Guru-RF/MicroPico/src/W5100/code.py

import board
import busio
import digitalio
import time
from adafruit_wiznet5k.adafruit_wiznet5k import WIZNET5K

##SPI0
SPI0_RX = board.GP16
SPI0_CSn = board.GP17
SPI0_SCK = board.GP18
SPI0_TX = board.GP19

##reset
W5x00_RSTn = board.GP20

print("Wiznet5k Ping Test (no DHCP)")

# Setup your network configuration below
# random MAC, later should change this value on your vendor ID
MY_MAC = (0x00, 0x03, 0x03, 0x03, 0x04, 0x05)
IP_ADDRESS = (172, 16, 30, 4)
SUBNET_MASK = (255, 255, 255, 0)
GATEWAY_ADDRESS = (172, 16, 30, 1)
DNS_SERVER = (8, 8, 8, 8)

#led = digitalio.DigitalInOut(board.GP25)
#led.direction = digitalio.Direction.OUTPUT

ethernetRst = digitalio.DigitalInOut(W5x00_RSTn)
ethernetRst.direction = digitalio.Direction.OUTPUT

# For Adafruit Ethernet FeatherWing
cs = digitalio.DigitalInOut(SPI0_CSn)
# For Particle Ethernet FeatherWing
# cs = digitalio.DigitalInOut(board.D5)
spi_bus = busio.SPI(SPI0_SCK, MOSI=SPI0_TX, MISO=SPI0_RX)

# Reset W5500 first
ethernetRst.value = False
time.sleep(1)
ethernetRst.value = True

# Initialize ethernet interface with DHCP
# eth = WIZNET5K(spi_bus, cs)
# Initialize ethernet interface without DHCP
eth = WIZNET5K(spi_bus, cs, is_dhcp=False, mac=MY_MAC)

# Set network configuration
eth.ifconfig = (IP_ADDRESS, SUBNET_MASK, GATEWAY_ADDRESS, DNS_SERVER)

print("Chip Version:", eth.chip)
print("MAC Address:", [hex(i) for i in eth.mac_address])
print("My IP address is:", eth.pretty_ip(eth.ip_address))

while True:
#    led.value = not led.value
    time.sleep(1)

print("Done!")
