Guru-RF/MicroPico/src/BME680/code.py

import adafruit_bme680
import time
import busio
import board

# Create the I2C interface.
i2c = busio.I2C(scl=board.GP21, sda=board.GP20)
bme680 = adafruit_bme680.Adafruit_BME680_I2C(i2c)

# change this to match the location's pressure (hPa) at sea level
bme680.sea_level_pressure = 1013.25

while True:
    print("\nTemperature: %0.1f C" % bme680.temperature)
    print("Gas: %d ohm" % bme680.gas)
    print("Humidity: %0.1f %%" % bme680.relative_humidity)
    print("Pressure: %0.3f hPa" % bme680.pressure)
    print("Altitude = %0.2f meters" % bme680.altitude)

    time.sleep(2)
