Guru-RF/MicroPico/src/code.py

import supervisor
import asyncio
import time
import µPICO
import board
import usb_hid
import simpleio
from adafruit_hid.keyboard import Keyboard
from adafruit_hid.keyboard_layout_us import KeyboardLayoutUS
from adafruit_hid.keycode import Keycode
from adafruit_hid.consumer_control import ConsumerControl
from adafruit_hid.consumer_control_code import ConsumerControlCode
from rainbowio import colorwheel

import terminalio
import displayio
import busio
from adafruit_display_text import label
from adafruit_ssd1351 import SSD1351

# Release any resources currently in use for the displays
displayio.release_displays()

spi = busio.SPI(board.GP18, board.GP19, board.GP16)

tft_cs = board.GP20
tft_dc = board.GP21

display_bus = displayio.FourWire(
    spi, command=tft_dc, chip_select=tft_cs, reset=board.GP22, baudrate=16000000
)

display = SSD1351(display_bus, width=128, height=128, rotation=0)


async def buttonTask(cc):
    while (True):
        await asyncio.sleep(0.1)
        if µPICO.buttonLeft.value is False:
            print("ButtonLeft Pressed!")
            cc.send(ConsumerControlCode.VOLUME_INCREMENT)
        if µPICO.buttonRight.value is False:
            print("ButtonRight Pressed!")
            cc.send(ConsumerControlCode.VOLUME_DECREMENT)

async def buzzerTask():
    while (True):
        simpleio.tone(board.GP10, 330, duration=0.25)
        simpleio.tone(board.GP10, 349, duration=0.25)
        simpleio.tone(board.GP10, 392, duration=0.25)
        simpleio.tone(board.GP10, 523, duration=0.5)
        await asyncio.sleep(0.5)
        simpleio.tone(board.GP10, 294, duration=0.25)
        simpleio.tone(board.GP10, 330, duration=0.25)
        simpleio.tone(board.GP10, 349, duration=0.5)
        await asyncio.sleep(0.5)
        simpleio.tone(board.GP10, 392, duration=0.25)
        simpleio.tone(board.GP10, 440, duration=0.25)
        simpleio.tone(board.GP10, 494, duration=0.25)
        simpleio.tone(board.GP10, 698, duration=0.5)
	await asyncio.sleep(0.5)
        simpleio.tone(board.GP10, 440, duration=0.25)
        simpleio.tone(board.GP10, 494, duration=0.25)
        simpleio.tone(board.GP10, 523, duration=0.5)
        simpleio.tone(board.GP10, 587, duration=0.5)
        simpleio.tone(board.GP10, 659, duration=0.5)
	await asyncio.sleep(0.5)
        simpleio.tone(board.GP10, 330, duration=0.25)
        simpleio.tone(board.GP10, 349, duration=0.25)
        simpleio.tone(board.GP10, 392, duration=0.25)
        simpleio.tone(board.GP10, 523, duration=0.5)
        await asyncio.sleep(0.5)
        simpleio.tone(board.GP10, 294, duration=0.25)
        simpleio.tone(board.GP10, 330, duration=0.25)
        simpleio.tone(board.GP10, 349, duration=0.5)
        await asyncio.sleep(0.5)
        simpleio.tone(board.GP10, 392, duration=0.25)
        simpleio.tone(board.GP10, 392, duration=0.25)
        simpleio.tone(board.GP10, 659, duration=0.5)
        simpleio.tone(board.GP10, 587, duration=0.5)
        await asyncio.sleep(0.5)
        simpleio.tone(board.GP10, 392, duration=0.25)
        simpleio.tone(board.GP10, 659, duration=0.5)
        simpleio.tone(board.GP10, 587, duration=0.5)
        await asyncio.sleep(0.5)
        simpleio.tone(board.GP10, 392, duration=0.25)
        simpleio.tone(board.GP10, 659, duration=0.5)
        simpleio.tone(board.GP10, 587, duration=0.5)
        simpleio.tone(board.GP10, 523, duration=0.5)

        await asyncio.sleep(120)

async def blinkyTask():
    while (True):
	for i in range(255):
		i = (i + 1) % 256
		µPICO.RGBled1.color = colorwheel(i)
		await asyncio.sleep(0.01)

async def blinkyTaskTwo():
    while (True):
	for i in range(255):
		i = (i + 1) % 256
		µPICO.RGBled2.color = colorwheel(i)
		await asyncio.sleep(0.01)

async def main():
    print("Intializing µPico")
    time.sleep(1)

    keyboard = Keyboard(usb_hid.devices)
    keyboard_layout = KeyboardLayoutUS(keyboard)
    cc = ConsumerControl(usb_hid.devices)
    time.sleep(1)

    print("Lets go async !")

    loop = asyncio.get_event_loop()
    button_task = asyncio.create_task(buttonTask(cc))
    blinky_task = asyncio.create_task(blinkyTask())
    blinky_task_two = asyncio.create_task(blinkyTaskTwo())
    buzzer_task = asyncio.create_task(buzzerTask())

    loop.run_until_complete(button_task)
    loop.close()


asyncio.run(main())
